xgiralt64/MP1584EN-Kicad-Template-Module/assets/20260708_193858.png

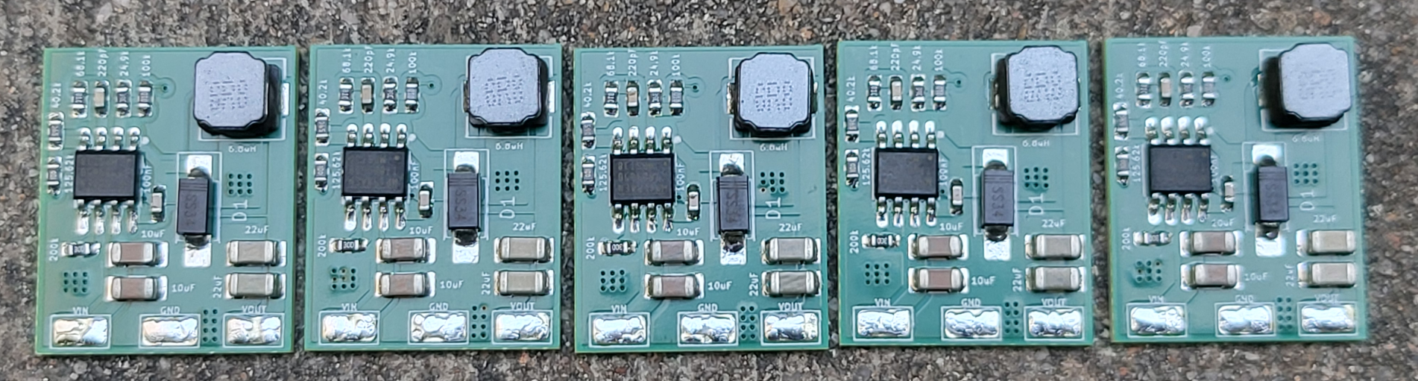
assets/20260708_193858.png
